imran9ahmed/ME366_Project_CarromBOT/Photo_dump/Group_Photo_2.JPG

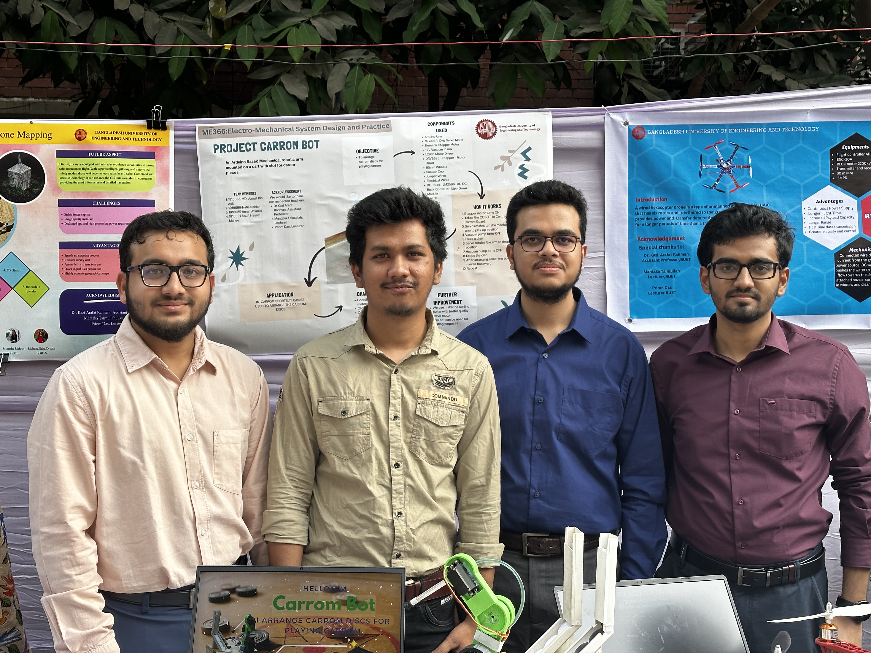
Photo_dump/Group_Photo_2.JPG
