imran9ahmed/ME366_Project_CarromBOT/Photo_dump/Me_With_Project.jpg

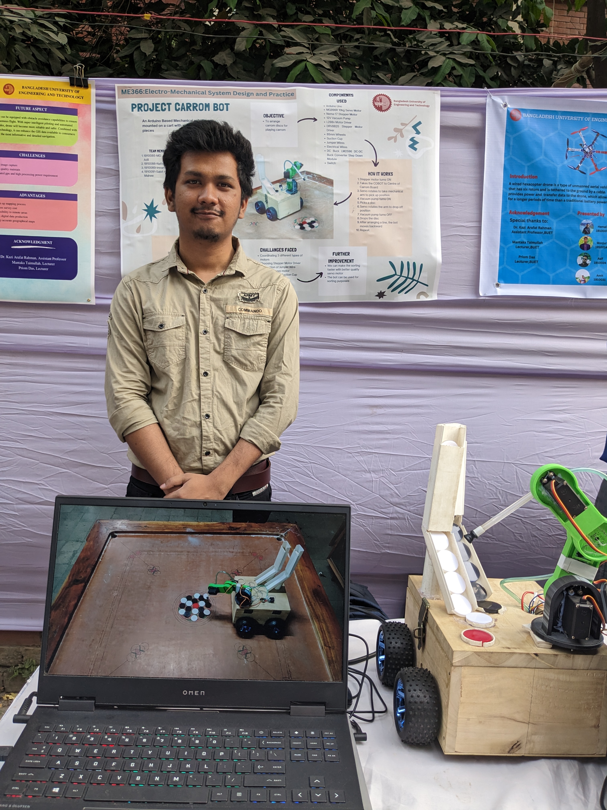
Photo_dump/Me_With_Project.jpg
