imran9ahmed/ME366_Project_CarromBOT/SOLIDWORKS/Photos/Lid.png

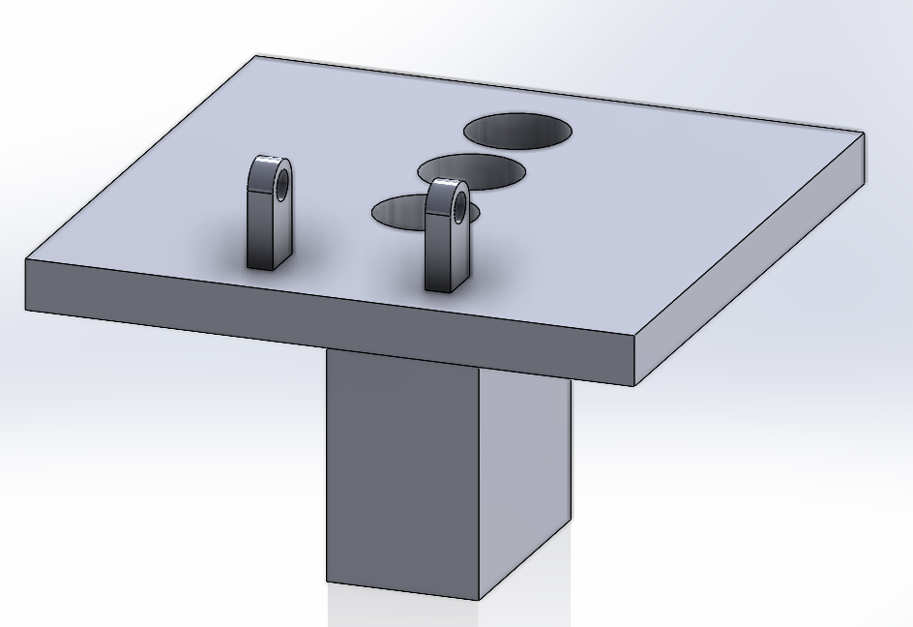
SOLIDWORKS/Photos/Lid.png
