imran9ahmed/ME366_Project_CarromBOT/SOLIDWORKS/Photos/0_CarromBoT_Assembly.png

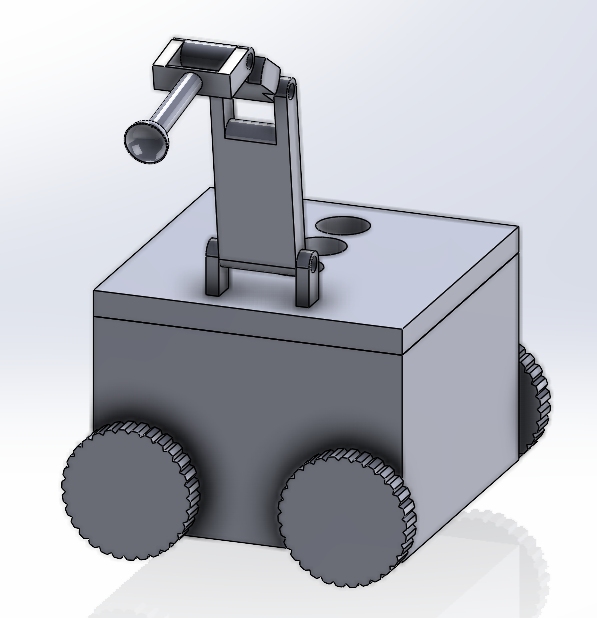
SOLIDWORKS/Photos/0_CarromBoT_Assembly.png
